omar-elmeteny/ArduinoCar/remote/lightSensor.cpp

#include <Arduino.h>

#include "common.h"
#include "lightSensor.h"

void setupLightSensor() {
  pinMode(45, OUTPUT);
  pinMode(A13, INPUT);
}

float getLightIntensity() {
  float value = analogRead(LDR_SENSOR);         //Reads the Value of LDR(light).
  #ifdef DEBUG
  Serial.print("LDR value is :");  //Prints the value of LDR to Serial Monitor.
  Serial.println(value);
  #endif
  return value;
}
