omar-elmeteny/ArduinoCar/bluetooth_at/bluetooth_at.ino

#include <SoftwareSerial.h>
SoftwareSerial BTSerial (50,51);
void setup() {
  // put your setup code here, to run once:
  Serial.begin(38400);
  Serial.println("Enter AT Commands");
  BTSerial.begin(38400);
}

void loop() {
  // put your main code here, to run repeatedly:
  if(BTSerial.available()){
    Serial.write(BTSerial.read());
  }
  if(Serial.available()){
    BTSerial.write(Serial.read());
  }
}
