omar-elmeteny/ArduinoCar/buzzer/buzzer.ino

const int buzzer = 13; //buzzer to arduino pin 9

void setup(){
  pinMode(buzzer, OUTPUT); // Set buzzer - pin 9 as an output
}

void loop(){
  tone(buzzer, 2000); // Send 1KHz sound signal...
  delay(200);        // ...for 1 sec
  noTone(buzzer);     // Stop sound...
  delay(200);        // ...for 1sec
}
