omar-elmeteny/ArduinoCar/car/buzzer.h

#ifndef Buzzer_h
#define Buzzer_h

void setupBuzzer();

#define DELAY_MEDIUM 1000
#define DELAY_CLOSE  500
#define DELAY_VERY_CLOSE 200
#define BUZZER_PIN  A0

#define BUZZER_FREQUENCY 500

#endif
